kaustubhshan27/arduino-uno-rev-3-clone/28pins_Project_V1I1/!Released Files/Step 2 - Board Assembly/Variant2_5V AND 3V3/28pins_Top View_5V AND 3V3.PDF

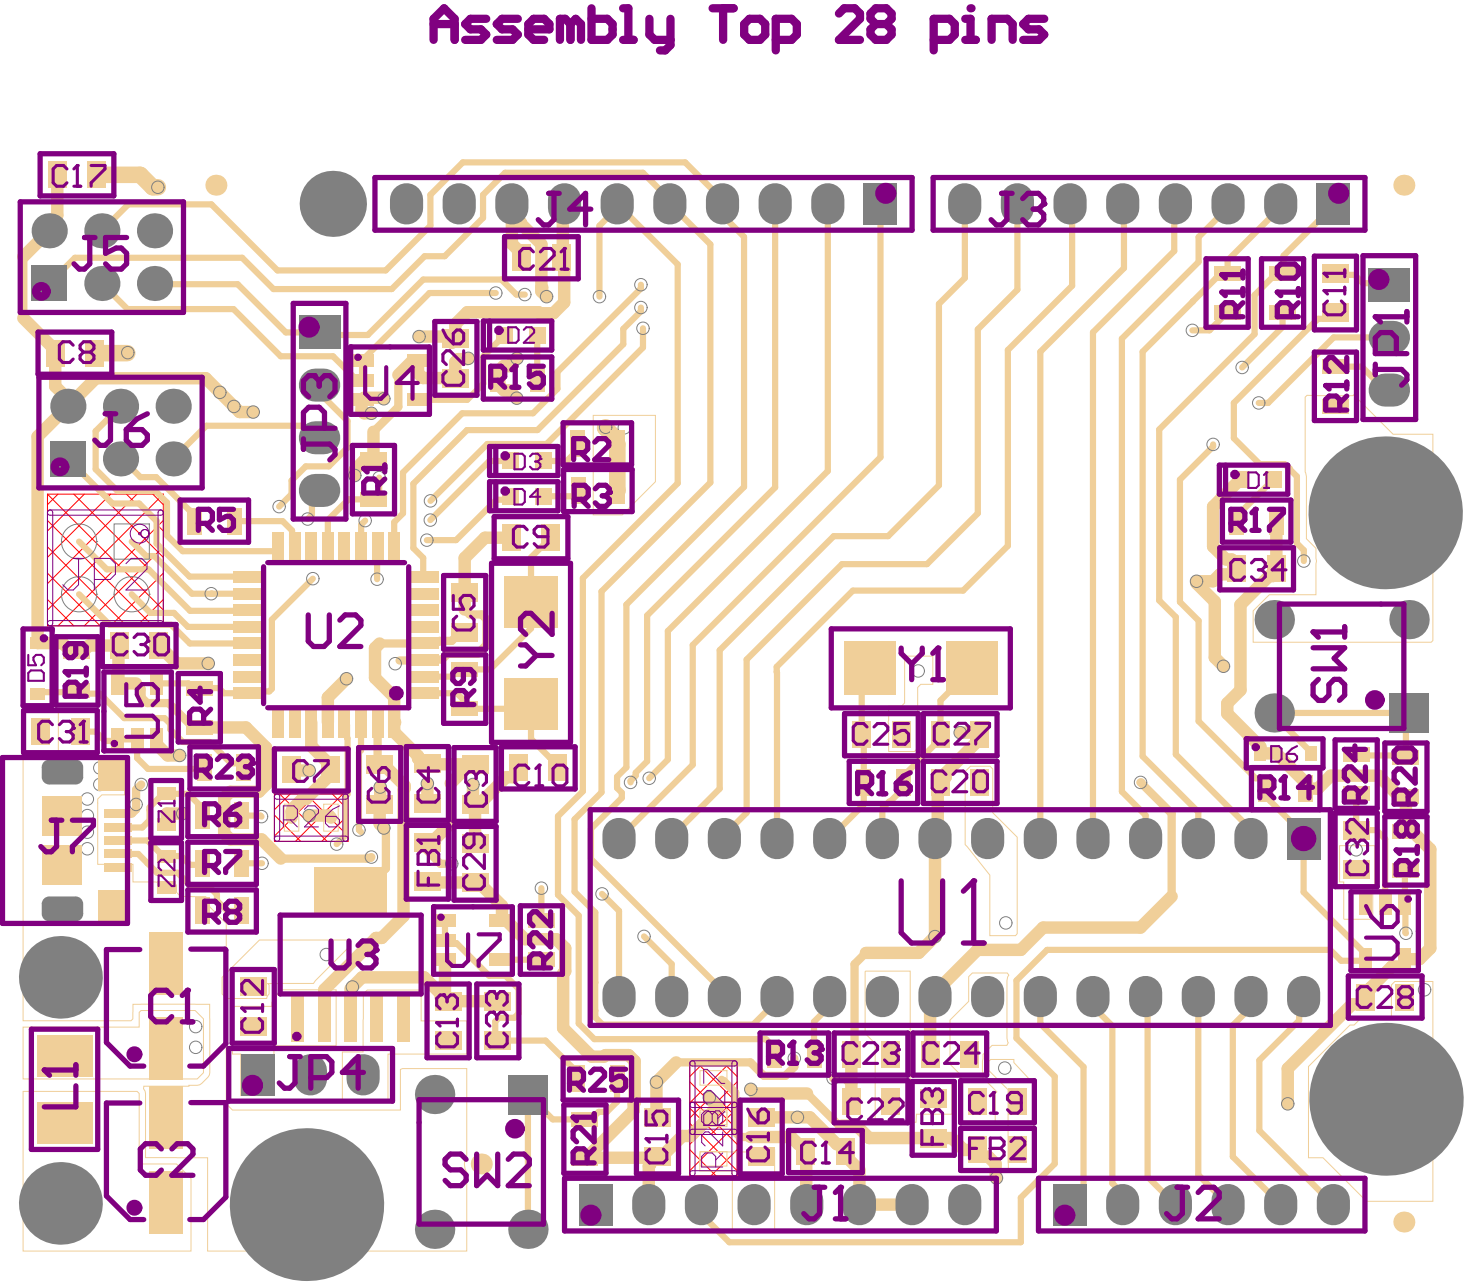
[picture p8: page 1]
